JurCag/NB_IoT_app/Sensor_Boards_FW/sensor_board_current/src/nbiot_ble_mesh_node_acs712.c

#include "nbiot_ble_mesh_node_acs712.h"

#define SENSOR_NAME                 ("Acs712")

NET_BUF_SIMPLE_DEFINE_STATIC(dcCurrentSensorData, 4);

/* Sensor Property ID based on sensor */
#define SENSOR_PROPERTY_ID_0        NBIOT_BLE_MESH_PROP_ID_DC_CURRENT

static NbiotSensorSetup_t sensorNbiotSetup[] = 
{
    {
        .name           = SENSOR_NAME,
        .propName       = "current",
        .propDataType   = NBIOT_FLOAT,
        .mmtUnit        = "A"
    }
};

static void updateNodeData(void);


static esp_ble_mesh_sensor_state_t nodeSensorStates[] =
{
    {
        .sensor_property_id = SENSOR_PROPERTY_ID_0,
        .descriptor.positive_tolerance = SENSOR_POSITIVE_TOLERANCE,
        .descriptor.negative_tolerance = SENSOR_NEGATIVE_TOLERANCE,
        .descriptor.sampling_function = SENSOR_SAMPLE_FUNCTION,
        .descriptor.measure_period = SENSOR_MEASURE_PERIOD,
        .descriptor.update_interval = SENSOR_UPDATE_INTERVAL,
        .sensor_data.format = ESP_BLE_MESH_SENSOR_DATA_FORMAT_A,
        .sensor_data.length = 0x03,
        .sensor_data.raw_value = &dcCurrentSensorData,
    }
};

/* BLE MESH MODELS */
// 1. Configuration Server Model
static esp_ble_mesh_cfg_srv_t configServer = 
{
    .relay = ESP_BLE_MESH_RELAY_ENABLED,
    .beacon = ESP_BLE_MESH_BEACON_ENABLED,
#if defined(CONFIG_BLE_MESH_FRIEND)
    .friend_state = ESP_BLE_MESH_FRIEND_ENABLED,
#else
    .friend_state = ESP_BLE_MESH_FRIEND_NOT_SUPPORTED,
#endif
#if defined(CONFIG_BLE_MESH_GATT_PROXY_SERVER)
    .gatt_proxy = ESP_BLE_MESH_GATT_PROXY_ENABLED,
#else
    .gatt_proxy = ESP_BLE_MESH_GATT_PROXY_NOT_SUPPORTED,
#endif
    .default_ttl = 7,
    /* 3 transmissions with 20ms interval */
    .net_transmit = ESP_BLE_MESH_TRANSMIT(2, 20),
    .relay_retransmit = ESP_BLE_MESH_TRANSMIT(2, 20),
};

// 2. Sensor Server Model
// NOTE: change this: 20 octets is large enough to hold two Sensor Descriptor state values
ESP_BLE_MESH_MODEL_PUB_DEFINE(sensorServerPub, 20, ROLE_NODE);
static esp_ble_mesh_sensor_srv_t sensorServer =
{
    .rsp_ctrl.get_auto_rsp = ESP_BLE_MESH_SERVER_RSP_BY_APP,
    .rsp_ctrl.set_auto_rsp = ESP_BLE_MESH_SERVER_RSP_BY_APP,
    .state_count = ARRAY_SIZE(nodeSensorStates),
    .states = nodeSensorStates,
};

// 3. Sensor Setup Server Model
ESP_BLE_MESH_MODEL_PUB_DEFINE(sensorSetupServerPub, 20, ROLE_NODE);
static esp_ble_mesh_sensor_srv_t sensorSetupServer =
{
    .rsp_ctrl.get_auto_rsp = ESP_BLE_MESH_SERVER_RSP_BY_APP,
    .rsp_ctrl.set_auto_rsp = ESP_BLE_MESH_SERVER_RSP_BY_APP,
    .state_count = ARRAY_SIZE(nodeSensorStates),
    .states = nodeSensorStates,
};

static esp_ble_mesh_model_t rootModels[] = 
{
    ESP_BLE_MESH_MODEL_CFG_SRV(&configServer),
    ESP_BLE_MESH_MODEL_SENSOR_SRV(&sensorServerPub, &sensorServer),
    ESP_BLE_MESH_MODEL_SENSOR_SETUP_SRV(&sensorSetupServerPub, &sensorSetupServer),
};

static esp_ble_mesh_elem_t elements[] = 
{
    ESP_BLE_MESH_ELEMENT(0, rootModels, ESP_BLE_MESH_MODEL_NONE),
};

static esp_ble_mesh_comp_t composition = 
{
    .cid = CID_ESP,
    .elements = elements,
    .element_count = ARRAY_SIZE(elements),
};

static esp_ble_mesh_prov_t provision = 
{
    .uuid = devUUID,
};

void nbiotBleMeshNodeAcs712Main(void)
{
    // Init sensor states, prosivion and composition of this node
    nbiotBleMeshServerInitSensorStates(nodeSensorStates, ARRAY_SIZE(nodeSensorStates));
    nbiotBleMeshServerInitProvision(&provision);
    nbiotBleMeshServerInitComposition(&composition);
    nbiotBleMeshServerInitSensorSetup(sensorNbiotSetup, sizeof(sensorNbiotSetup)/sizeof(sensorNbiotSetup[0]));

    // Register CallBack which updates the node data from sensor
    nbiotBleMeshRegisterUpdateSensorDataCB(updateNodeData);

    // Start BLE Mesh Server
    nbiotBleMeshServerMain();

    // Start Sensor Measurement
    sensorAcs712CreateTaskDataAcq();
}

// This function is unique based on the sensor
static void updateNodeData(void)
{
    static const char* tag = "ACS712";
    static float dcCurrent;
    uint8_t i;

    dcCurrent = sensorAcs712GetCurrent();

    // NOTE: Very important to reset the net buffer beffore pushing new data,
    // otherwise it causes unpredictable behaviour.
    i = 0;
    net_buf_simple_reset(&dcCurrentSensorData);
    net_buf_simple_push_le32(&dcCurrentSensorData, *(uint32_t*)(&dcCurrent));
    ESP_LOGI(tag, "[%s] value: [%f], units [%s]", sensorNbiotSetup[i].propName, dcCurrent, sensorNbiotSetup[i].mmtUnit);
}
