JurCag/NB_IoT_app/Sensor_Boards_FW/sensor_board_current/include/nbiot_ble_mesh_node_acs712.h

#ifndef __NBIOT_BLE_MESH_NODE_ACS712_H__
#define __NBIOT_BLE_MESH_NODE_ACS712_H__

#include "server_include/nbiot_ble_mesh_server.h"
#include "sensor_acs712.h"

void nbiotBleMeshNodeAcs712Main(void);

#endif // __NBIOT_BLE_MESH_NODE_ACS712_H__
