JurCag/NB_IoT_app/Master_Board_FW/concentrator_pcb_rev_1_0/include/BG96_mqtt.h

#ifndef __BG96_MQTT_H__
#define __BG96_MQTT_H__

#include "BG96_AT_cmds_core.h"
#include "uart.h"
#include "BG96.h"
#include "AT_cmds.h"
#include "freertos/timers.h"
#include "BG96_tcpip.h"
#include "board.h"

typedef SensorData_t PayloadData_t;

#define TOPIC_QUEUE_ITEM_SIZE           (64)
typedef struct
{
    char b[TOPIC_QUEUE_ITEM_SIZE];
} MqttTopic_t;

void BG96_mqttConfigParams(void);
void BG96_mqttRegisterAsyncCmds(void);
void BG96_mqttOpenConn(void);
void BG96_mqttCloseConn(void);
void BG96_mqttConnToServer(void);
void BG96_mqttCreateTaskReopenConnection(void);
void BG96_mqttPubQueuedData(void);
void BG96_mqttSubToTopic(char* subTopic);

void BG96_mqttCreatePayloadDataQueue(void);
void BG96_mqttQueuePayloadData(char* topic, PayloadData_t payloadData);

void BG96_checkIfConnectedToMqttServer(void);
uint8_t BG96_mqttResponseParser(BG96_AtPacket_t* packet, char* data);

#endif // __BG96_MQTT_H__
