JurCag/NB_IoT_app/Master_Board_FW/concentrator_pcb_rev_1_0/include/BG96_tcpip.h

#ifndef __BG96_TCPIP_H__
#define __BG96_TCPIP_H__

#include "BG96_AT_cmds_core.h"
#include "BG96.h"
#include "AT_cmds.h"

void BG96_tcpipConfigParams(void);
void BG96_tcpipActivatePDP(void);
void BG96_tcpipDeactivatePDP(void);
uint8_t BG96_tcpipResponseParser(BG96_AtPacket_t* packet, char* data);


#endif // __BG96_TCPIP_H__
