JurCag/NB_IoT_app/Sensor_Boards_FW/sensor_board_ph/include/nbiot_ble_mesh_node_4502c.h

#ifndef __NBIOT_BLE_MESH_NODE_4502C_H__
#define __NBIOT_BLE_MESH_NODE_4502C_H__

#include "server_include/nbiot_ble_mesh_server.h"
#include "sensor_4502c.h"

void nbiotBleMeshNodePh4502cMain(void);

#endif // __NBIOT_BLE_MESH_NODE_4502C_H__
