JurCag/NB_IoT_app/Sensor_Boards_FW/sensor_board_turbidity/include/nbiot_ble_mesh_node_ts300b.h

#ifndef __NBIOT_BLE_MESH_NODE_TS300B_H__
#define __NBIOT_BLE_MESH_NODE_TS300B_H__

#include "server_include/nbiot_ble_mesh_server.h"
#include "sensor_ts300b.h"

void nbiotBleMeshNodeTs300bMain(void);

#endif // __NBIOT_BLE_MESH_NODE_TS300B_H__
