JurCag/NB_IoT_app/Sensor_Boards_FW/sensor_board_co2/include/nbiot_ble_mesh_node_mhz19b.h

#ifndef __NBIOT_BLE_MESH_NODE_MHZ19B_H__
#define __NBIOT_BLE_MESH_NODE_MHZ19B_H__

#include "server_include/nbiot_ble_mesh_server.h"
#include "sensor_mhz19b.h"

void nbiotBleMeshNodeMhz19bMain(void);

#endif // __NBIOT_BLE_MESH_NODE_MHZ19B_H__
