JurCag/NB_IoT_app/Sensor_Boards_FW/sensor_board_photores/include/nbiot_ble_mesh_node_photores.h

#ifndef __NBIOT_BLE_MESH_NODE_PHOTORES_H__
#define __NBIOT_BLE_MESH_NODE_PHOTORES_H__

#include "server_include/nbiot_ble_mesh_server.h"
#include "sensor_photores.h"

void nbiotBleMeshNodePhotoresMain(void);

#endif // __NBIOT_BLE_MESH_NODE_PHOTORES_H__
