JurCag/NB_IoT_app/Sensor_Boards_FW/sensor_board_BME280/include/nbiot_ble_mesh_node_bme280.h

#ifndef __NBIOT_BLE_MESH_NODE_BME280_H__
#define __NBIOT_BLE_MESH_NODE_BME280_H__

#include "server_include/nbiot_ble_mesh_server.h"
#include "sensor_bme280.h"

void nbiotBleMeshNodeBme280Main(void);

#endif // __NBIOT_BLE_MESH_NODE_BME280_H__
