JurCag/NB_IoT_app/Master_Board_FW/concentrator_breadboard_demo/include/nbiot_ble_mesh_bg96_interface.h

#ifndef __NBIOT_BLE_MESH_BG96_INTERFACE_H__
#define __NBIOT_BLE_MESH_BG96_INTERFACE_H__

#include "nbiot_ble_mesh_provisioner_client.h"
#include "BG96.h"

void nbiotCreateTaskSensorDataGathering(void);
void nbiotSensorDataToBg96(uint16_t propId, uint8_t* data, uint8_t dataLen,  NbiotSensorSetup_t* setup);

#endif // __NBIOT_BLE_MESH_BG96_INTERFACE_H__
